khyale/nrf-board-v1/brd/oshpark/nrf-v1-board top.png

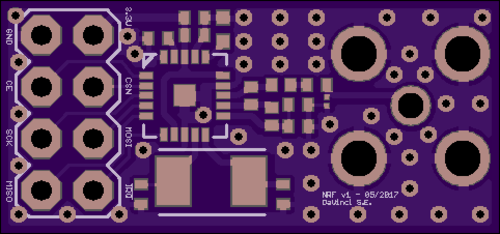
brd/oshpark/nrf-v1-board top.png
