khyale/nrf-board-v1/brd/oshpark/nrf-v1-toplayer.png

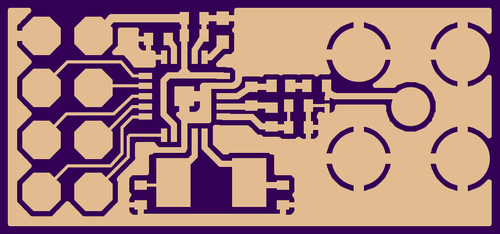
brd/oshpark/nrf-v1-toplayer.png
