khyale/nrf-board-v1/brd/oshpark/nrf-v1-bottomsoldermask.png

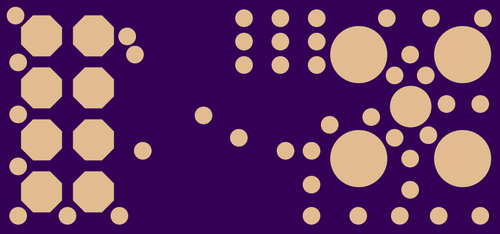
brd/oshpark/nrf-v1-bottomsoldermask.png
