khyale/nrf-board-v1/brd/oshpark/nrf-v1-topsoldermask.png

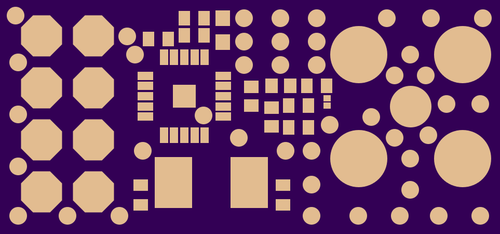
brd/oshpark/nrf-v1-topsoldermask.png
